Klocman/MSREG/Documentation/Photos/app1.png

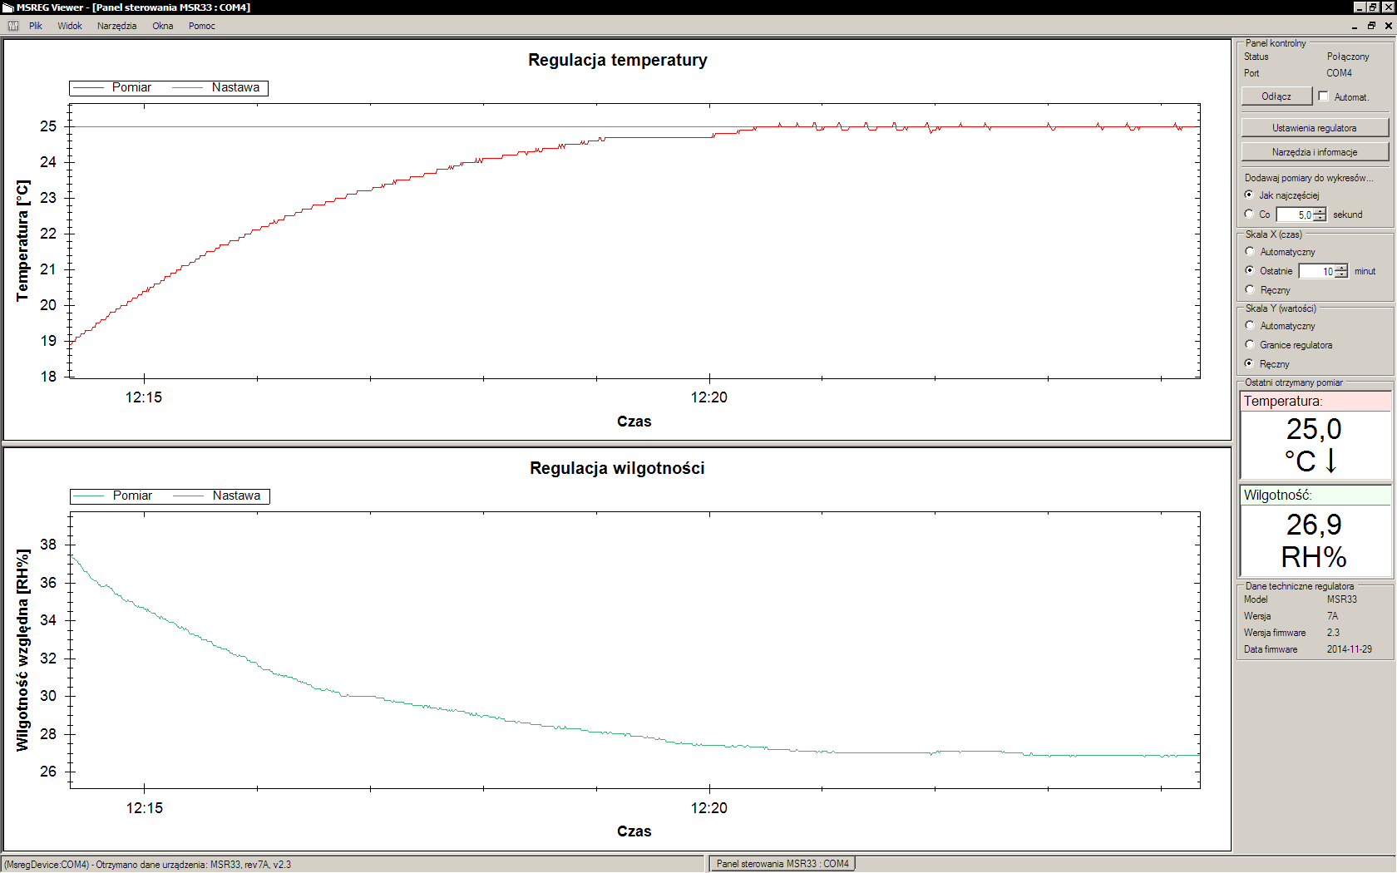
Documentation/Photos/app1.png
