Klocman/MSREG/Documentation/Photos/app2.png

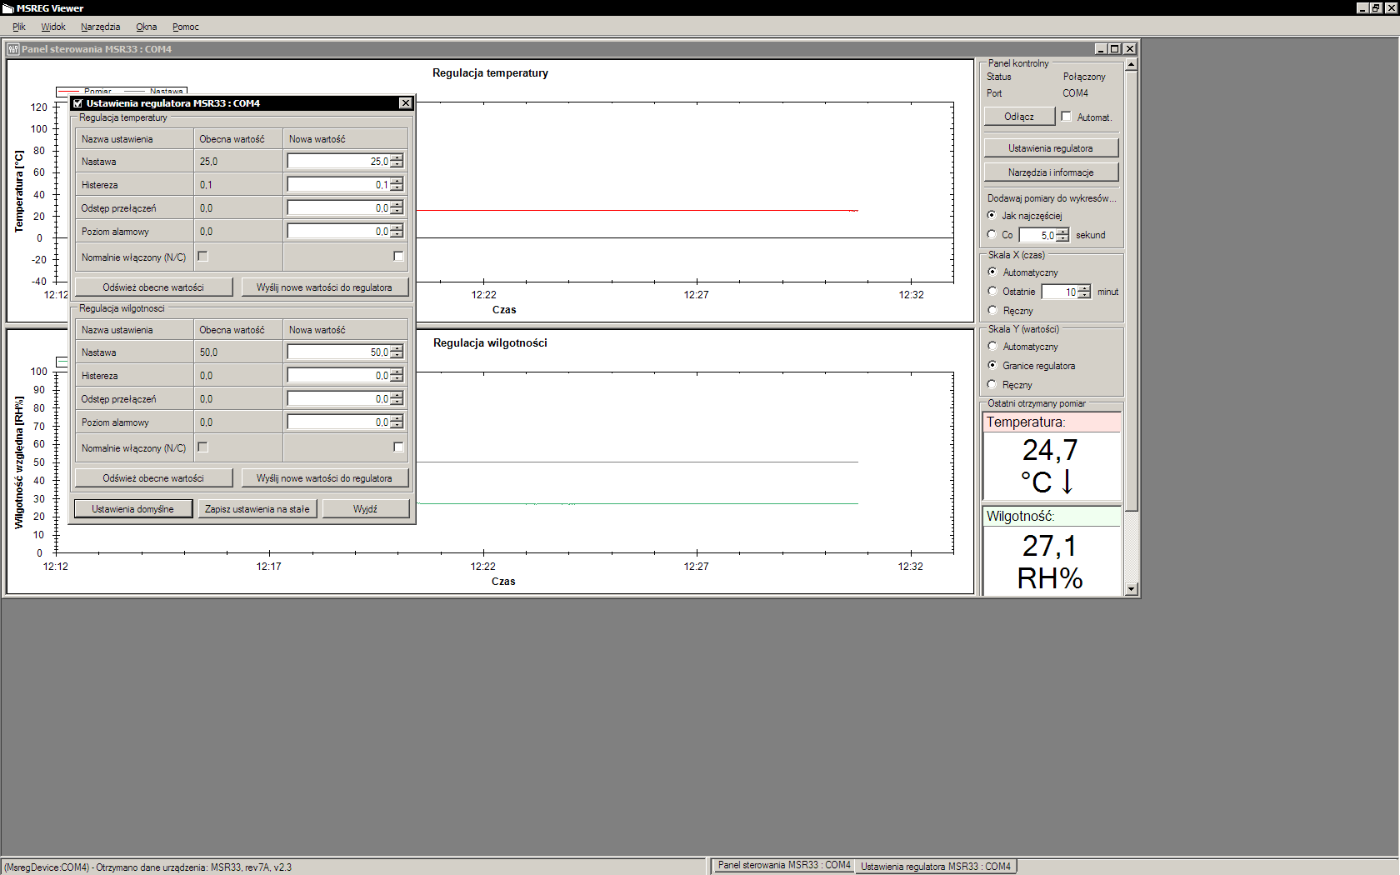
Documentation/Photos/app2.png
