Klocman/MSREG/Documentation/Photos/board_triacsplosion.jpg

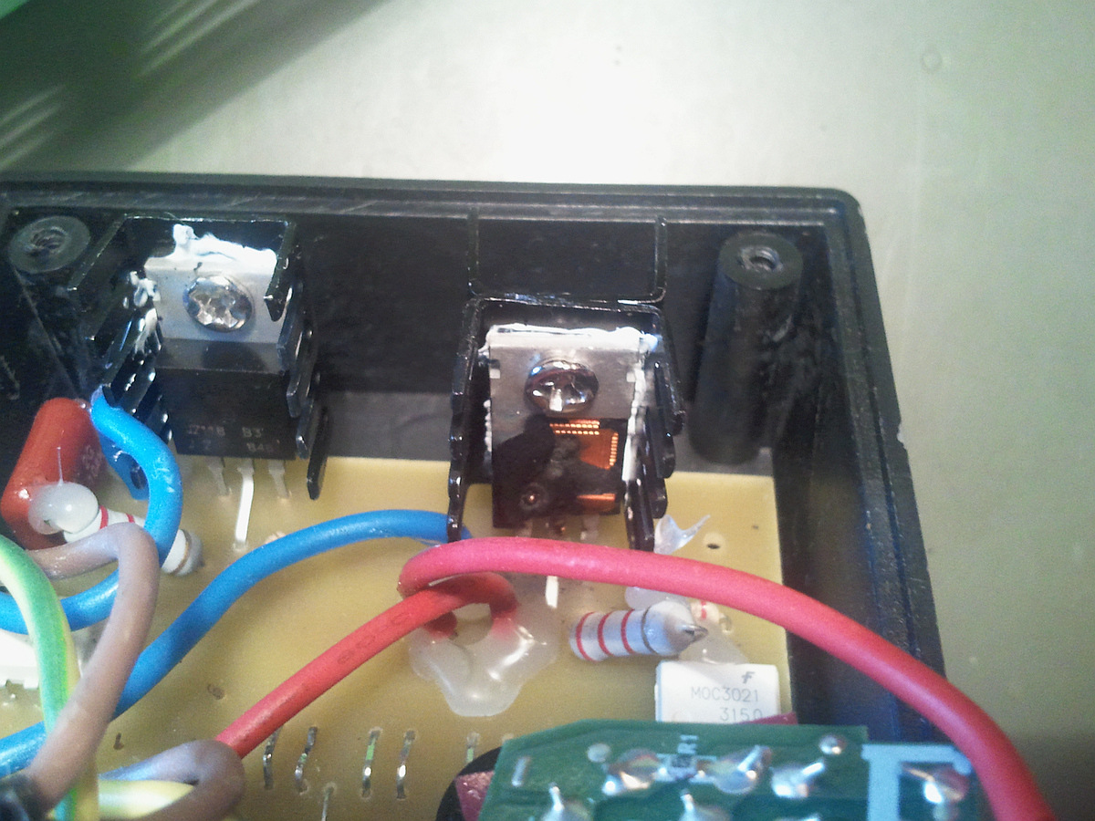
Documentation/Photos/board_triacsplosion.jpg
