Klocman/MSREG/Documentation/Photos/working4.jpg

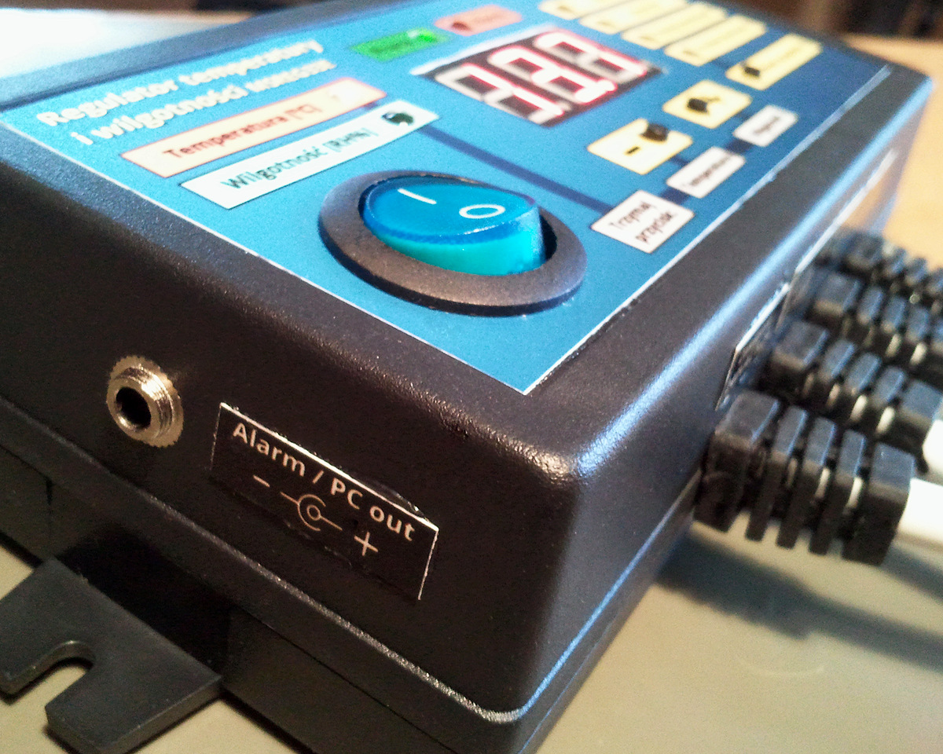
Documentation/Photos/working4.jpg
