Klocman/MSREG/Documentation/Photos/working5.jpg

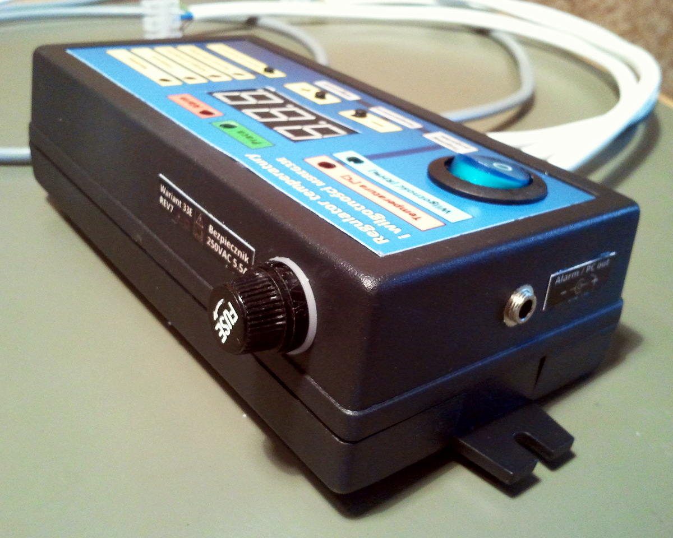
Documentation/Photos/working5.jpg
