Klocman/MSREG/Documentation/Photos/working7.jpg

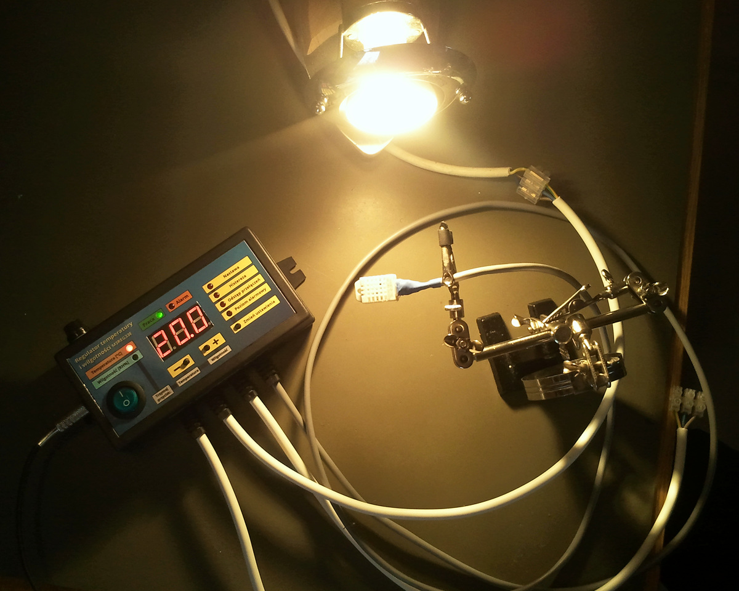
Documentation/Photos/working7.jpg
