Klocman/MSREG/MSREG Viewer/MSREG Viewer/Resources/aboutImage.png

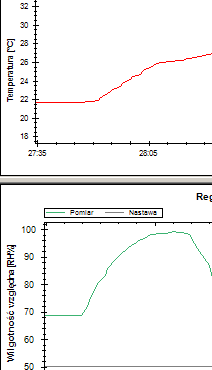
MSREG Viewer/MSREG Viewer/Resources/aboutImage.png
