Klocman/MSREG/Firmware/MSREG_universal/PinConfiguration.h

/*
 * PinConfiguration.h
 *
 * Created: 20-09-14 2:21:55 PM
 *  Author: Klocman
 */ 

#include "./Version/VersionInfo.h"

#ifdef REV7
#include "PinConfiguration_0.h"
#endif

#ifdef REV7A
#include "PinConfiguration_A.h"
#endif
